ARTS-Laboratory/Drone-Delivered-Camera/system_design/Upright-Camera/Media/IMG_3217.jpg

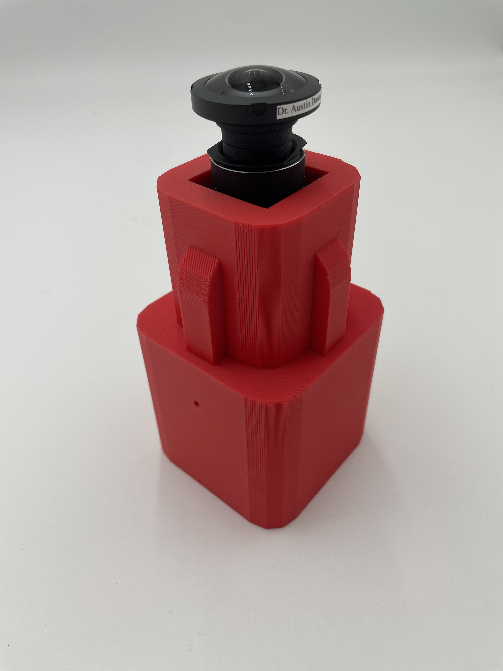
system_design/Upright-Camera/Media/IMG_3217.jpg
