ARTS-Laboratory/Drone-Delivered-Camera/system_design/Upright-Camera/Media/IMG_3219.jpg

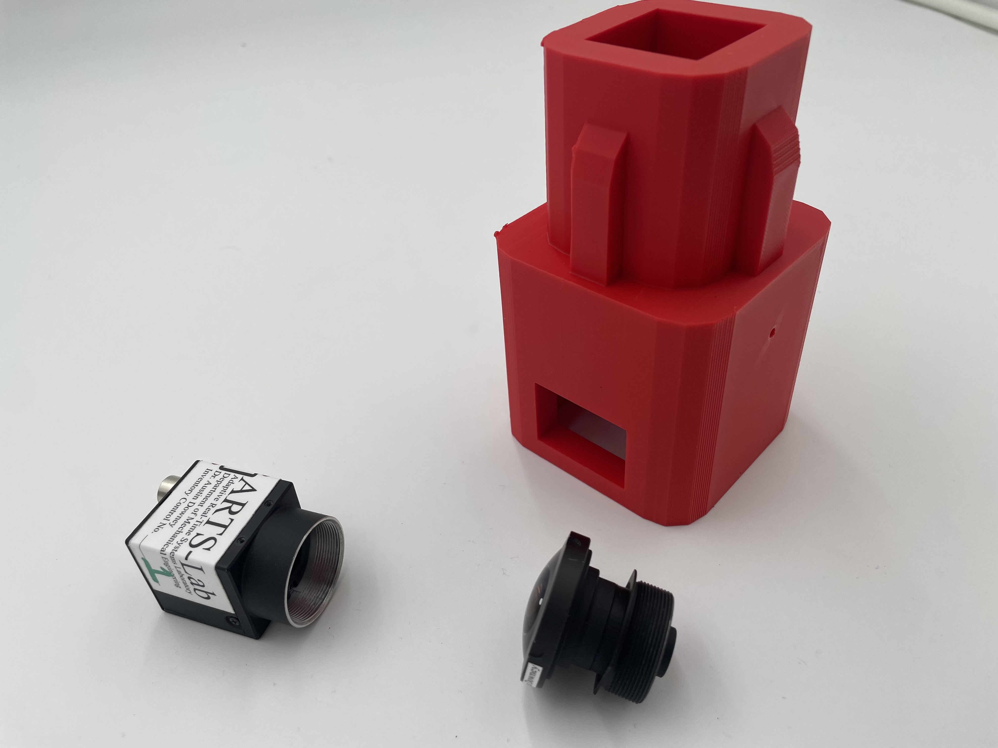
system_design/Upright-Camera/Media/IMG_3219.jpg
