ARTS-Laboratory/Drone-Delivered-Camera/system_design/Palomar/v3/Media/IMG_3113 (1).jpg

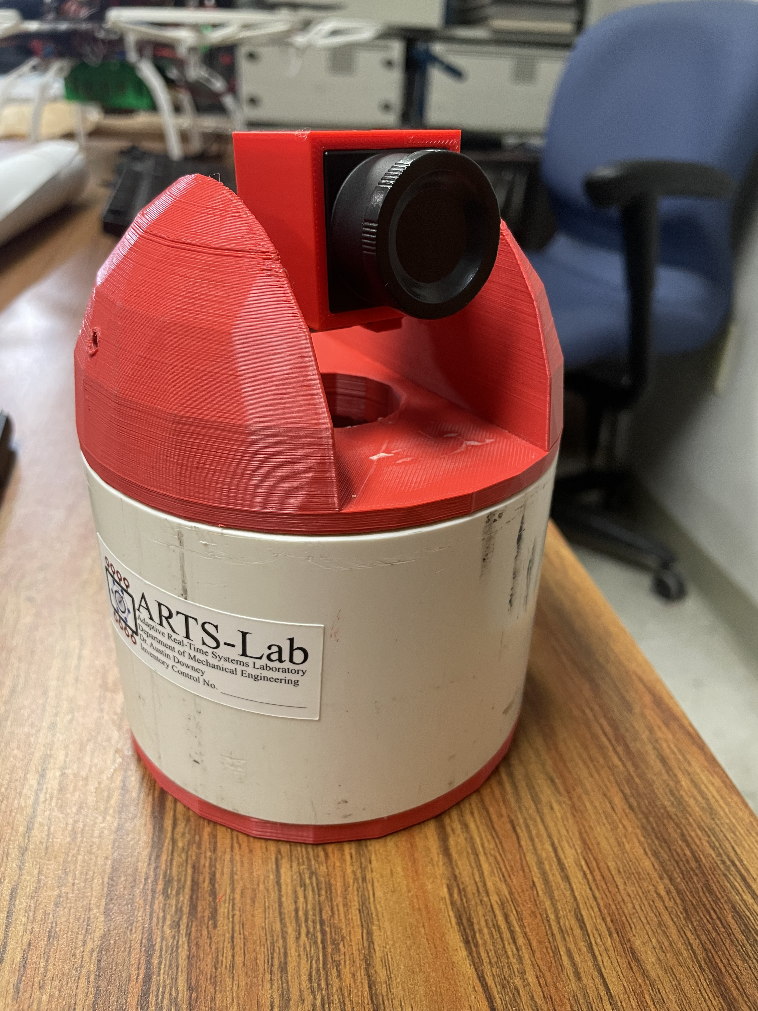
system_design/Palomar/v3/Media/IMG_3113 (1).jpg
